Allen-Synthesis/USB-Router/images/bg-18.jpg

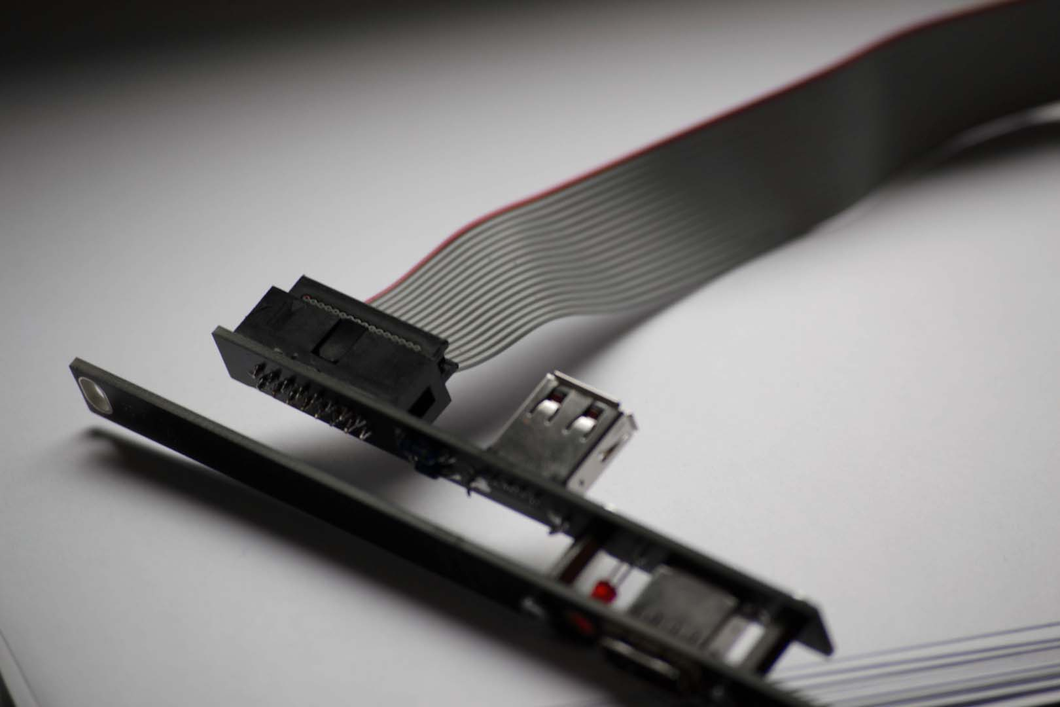
images/bg-18.jpg
