Allen-Synthesis/USB-Router/images/panel-pcb.jpg

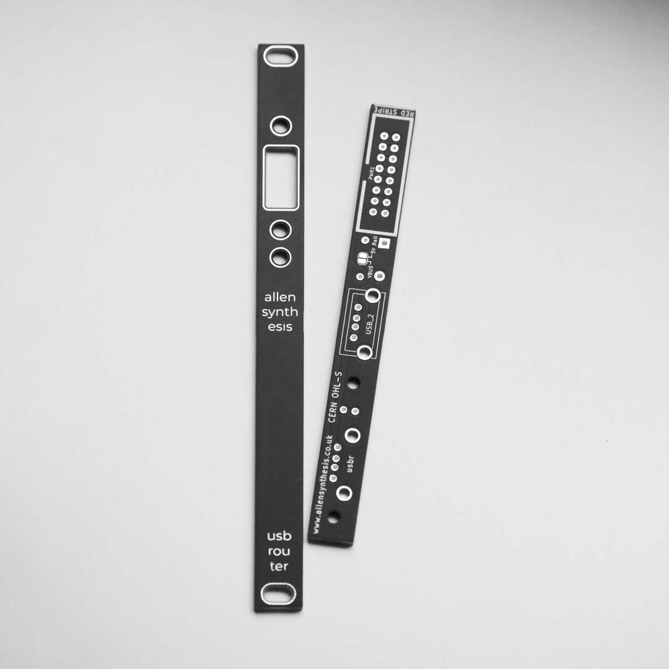
images/panel-pcb.jpg
