Allen-Synthesis/USB-Router/images/plugged-in-1.jpg

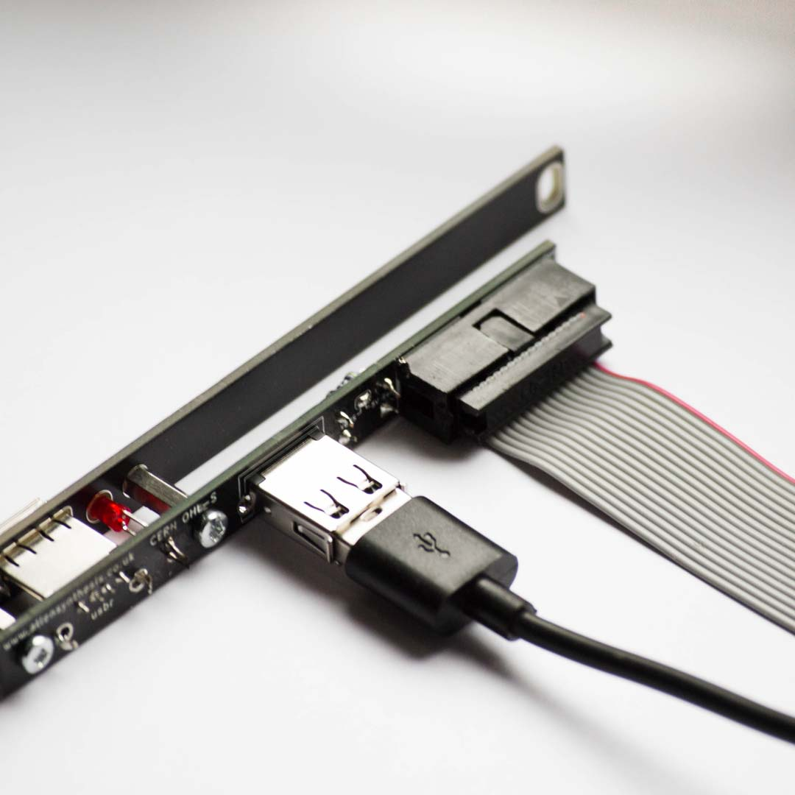
images/plugged-in-1.jpg
